v9938/MSX_SimpleCartridge/PCB/Image6.jpg

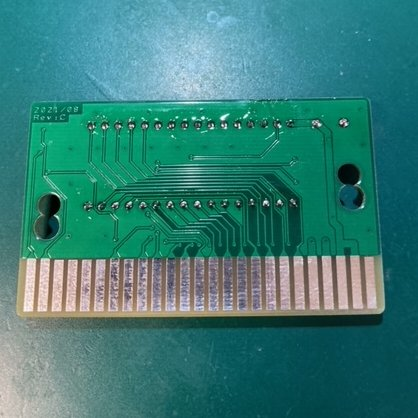
PCB/Image6.jpg
